nickyu42/flowmeter/stm32f4_firmware/src/config.h

#include "PinNames.h"

// LoRa constants
#define TX_DBM              14
#define BW_KHZ              125
#define SPREADING_FACTOR    7
#define CF_HZ               915000000

// Pin config
#define INA219_SDA  PB_9
#define INA219_SCLK PB_8
